somhi/MIDI2SBC/datasheets-info-pictures/addon-villena-2.jpg

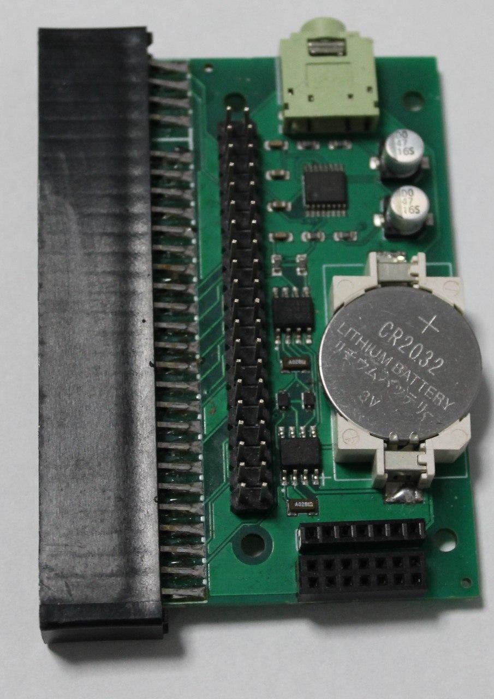
datasheets-info-pictures/addon-villena-2.jpg
