somhi/MIDI2SBC/datasheets-info-pictures/pcm5102_jack.jpg

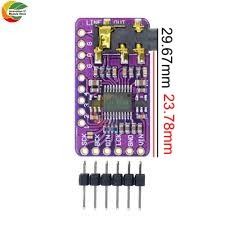
datasheets-info-pictures/pcm5102_jack.jpg
