somhi/MIDI2SBC/datasheets-info-pictures/pi-midi-Arana.jpg

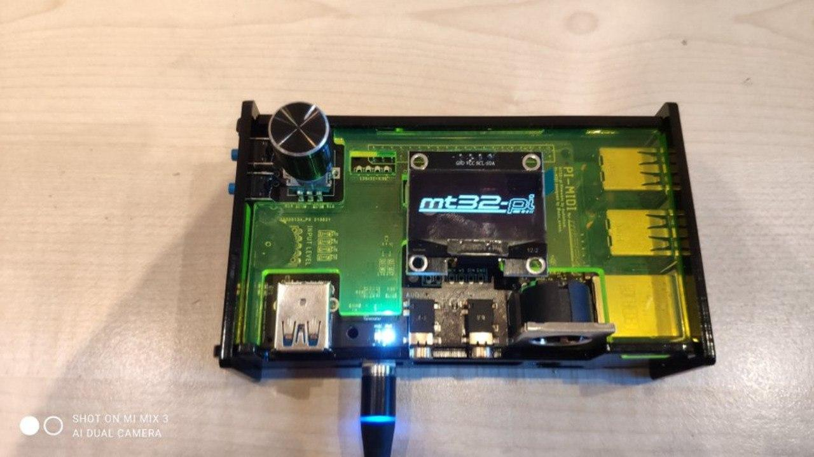
datasheets-info-pictures/pi-midi-Arana.jpg
