somhi/MIDI2SBC/datasheets-info-pictures/pmod-dvi.png

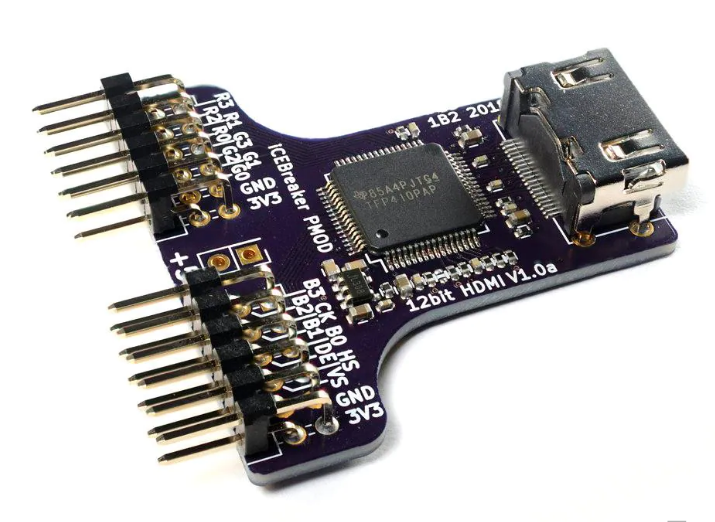
datasheets-info-pictures/pmod-dvi.png
