somhi/MIDI2SBC/datasheets-info-pictures/pmod-hyperram.png

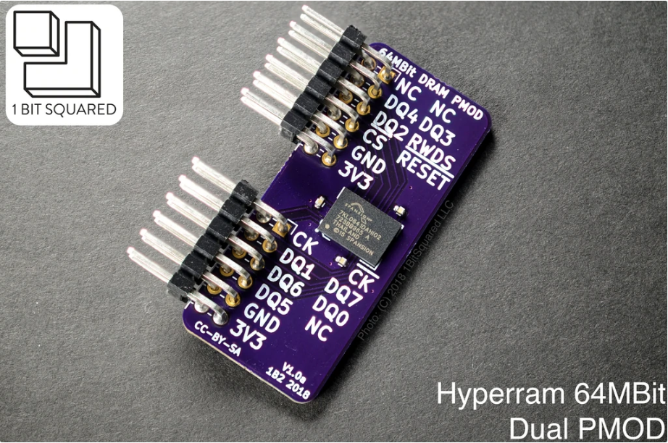
datasheets-info-pictures/pmod-hyperram.png
