somhi/MIDI2SBC/datasheets-info-pictures/pmod_vga.png

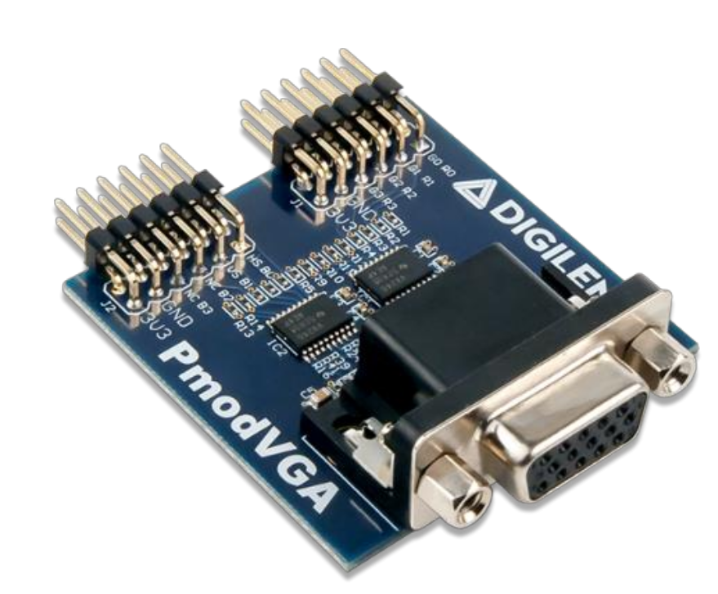
datasheets-info-pictures/pmod_vga.png
