somhi/MIDI2SBC/datasheets-info-pictures/NeptUNO_solder_pads.png

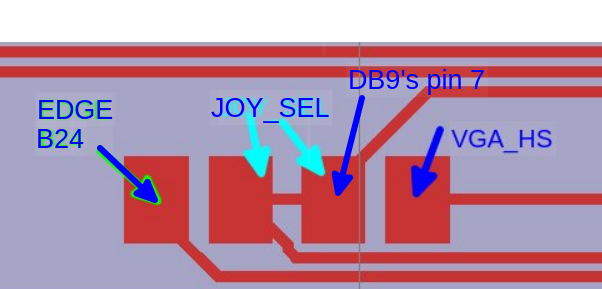
datasheets-info-pictures/NeptUNO_solder_pads.png
